ur8us/dsp-sinad-meter/KiCAD/SINAD-meter-KiCAD.kicad_sch

## KiCad design KiCAD/SINAD-meter-KiCAD.kicad_sch (2026-03-13)

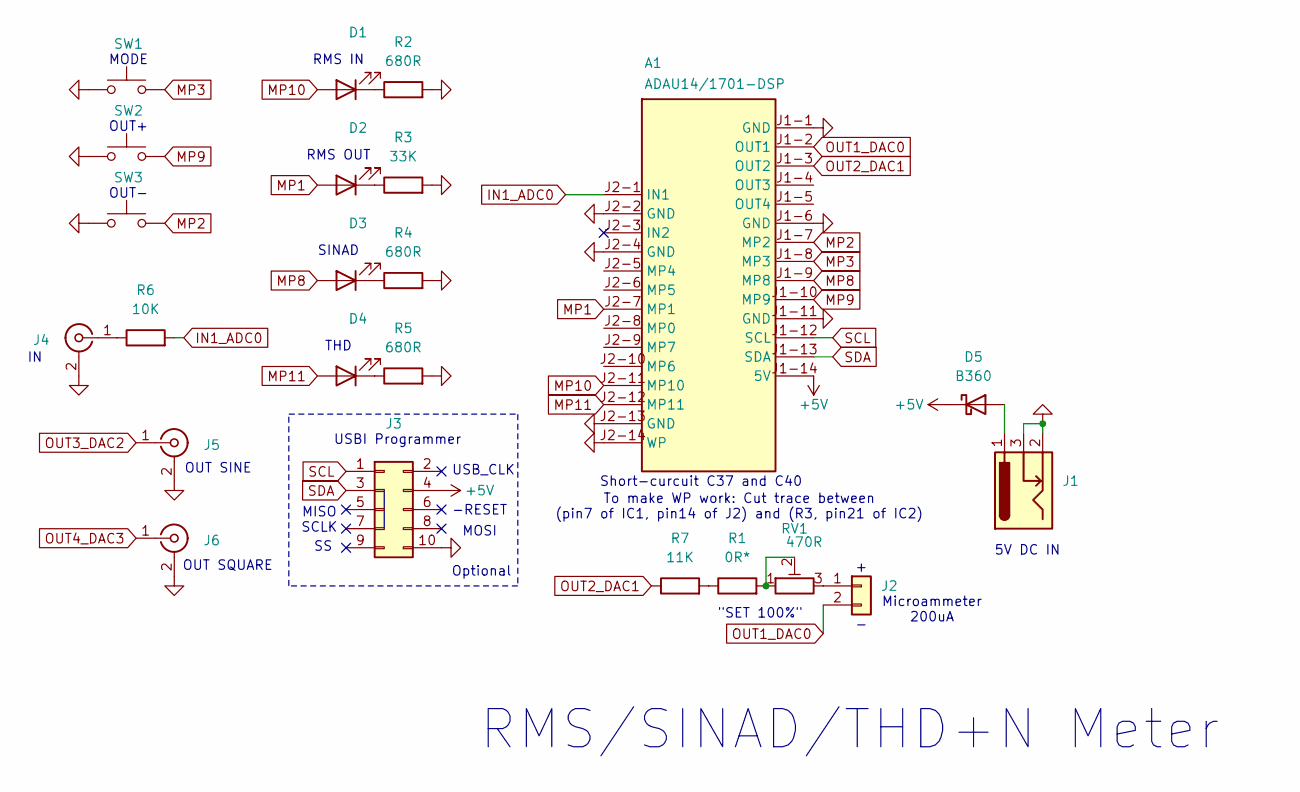
[picture p15: schematic SINAD-meter-KiCAD.kicad_sch]

Parts:
A1: ADAU14/1701-DSP
D1, D2, D3, D4: LED
D5: B360; D_SMC
J1: Barrel_Jack_Switch
J2: Conn_01x02
J3: Conn_02x05_Odd_Even
J4, J5, J6: Conn_Coaxial
R1: 0R*
R2, R4, R5: 680R
R3: 33K
R6: 10K
R7: 11K
RV1: 470R
SW1, SW2, SW3: SW_Push

Connections:
+5V: A1.J1-14 (5V), D5.1 (K), J3.4
GND: A1.J1-1 (GND), A1.J1-6 (GND), A1.J1-11 (GND), A1.J2-2 (GND), A1.J2-4 (GND), A1.J2-13 (GND), A1.J2-14 (WP), J1.2, J1.3, J3.10, J4.2 (Ext), J5.2 (Ext), J6.2 (Ext), R2.2, R3.2, R4.2, R5.2, SW1.1, SW2.1, SW3.1
IN1_ADC0: A1.J2-1 (IN1), R6.2
MP1: A1.J2-7 (MP1), D2.2 (A)
MP2: A1.J1-7 (MP2), SW3.2
MP3: A1.J1-8 (MP3), SW1.2
MP8: A1.J1-9 (MP8), D3.2 (A)
MP9: A1.J1-10 (MP9), SW2.2
MP10: A1.J2-11 (MP10), D1.2 (A)
MP11: A1.J2-12 (MP11), D4.2 (A)
unnamed: D1.1 (K), R2.1
unnamed: D2.1 (K), R3.1
unnamed: D3.1 (K), R4.1
unnamed: D4.1 (K), R5.1
unnamed: D5.2 (A), J1.1
unnamed: J2.1, RV1.3
unnamed: J4.1 (In), R6.1
unnamed: R1.1, R7.2
unnamed: R1.2, RV1.1, RV1.2
OUT1_DAC0: A1.J1-2 (OUT1), J2.2
OUT2_DAC1: A1.J1-3 (OUT2), R7.1
OUT3_DAC2: J5.1 (In)
OUT4_DAC3: J6.1 (In)
SCL: A1.J1-12 (SCL), J3.1
SDA: A1.J1-13 (SDA), J3.3

Notes on the sheet:
OUT-
To make WP work: Cut trace between (pin7 of IC1, pin14 of J2) and (R3, pin21 of IC2)
SCLK
MOSI
Short-curcuit C37 and C40
SINAD
USB_CLK
THD
OUT+
MODE
USBI Programmer
OUT SQUARE
RMS/SINAD/THD+N Meter
Optional
RMS OUT
Microammeter 200uA
"SET 100%"
MISO
RMS IN
-RESET
OUT SINE
5V DC IN
